heiso/macrolev/ref/lekker-switch-2.webp

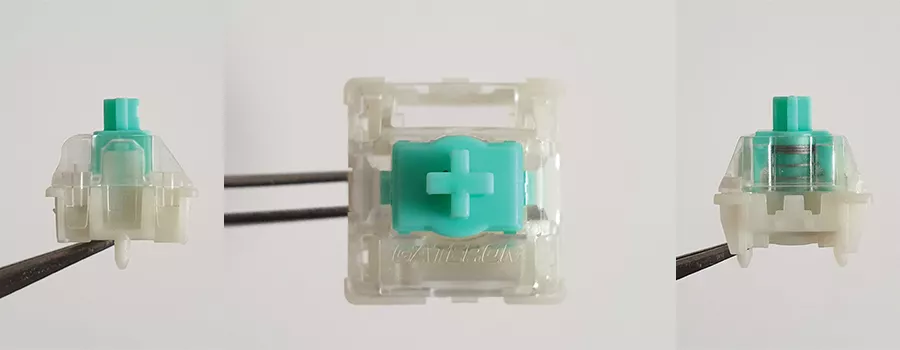
ref/lekker-switch-2.webp
