heiso/macrolev/ref/lekker-switch.png

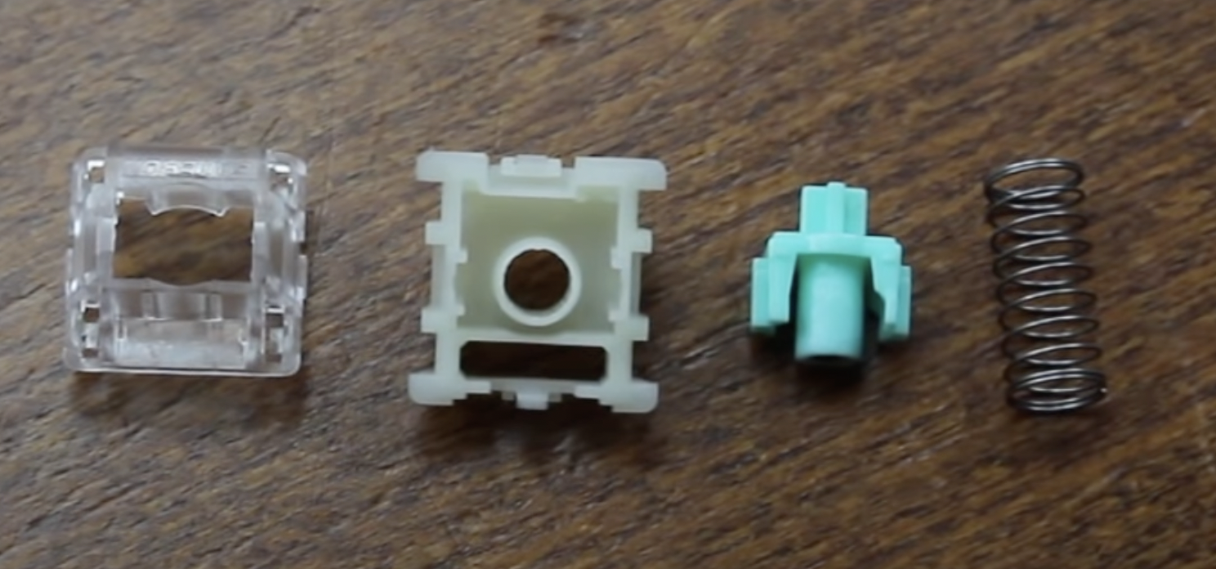
ref/lekker-switch.png
