heiso/macrolev/ref/Wooting-60HE/W60HE-01.jpg

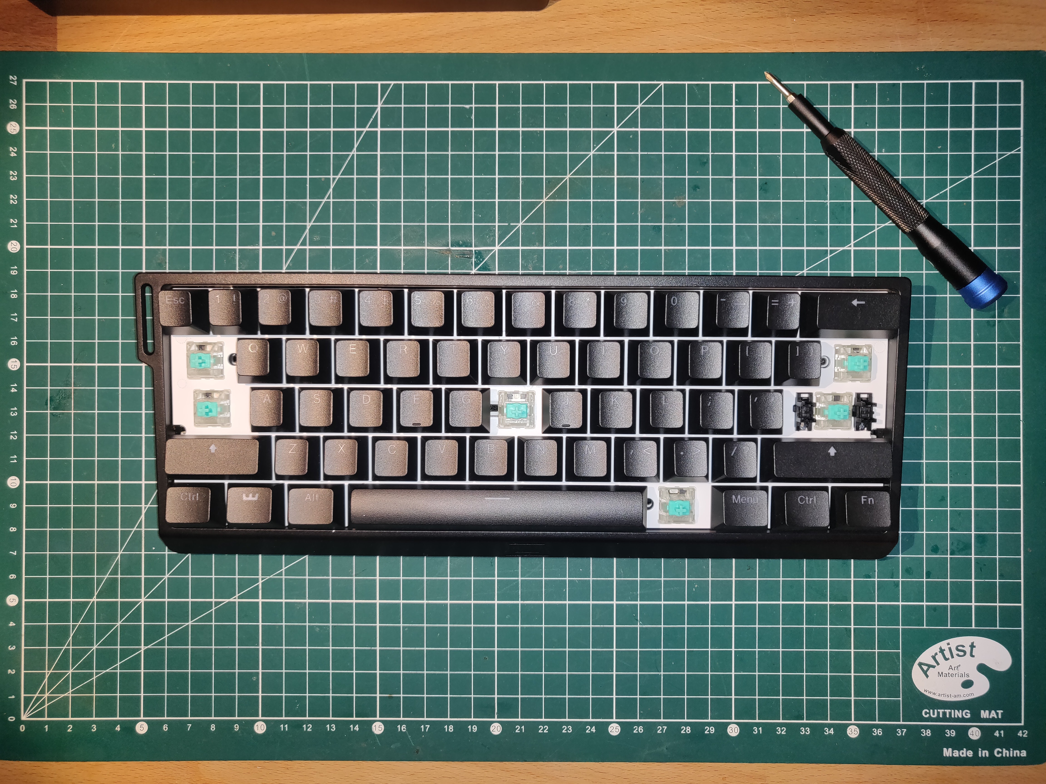
ref/Wooting-60HE/W60HE-01.jpg
