heiso/macrolev/ref/Wooting-60HE/W60HE-02.jpg

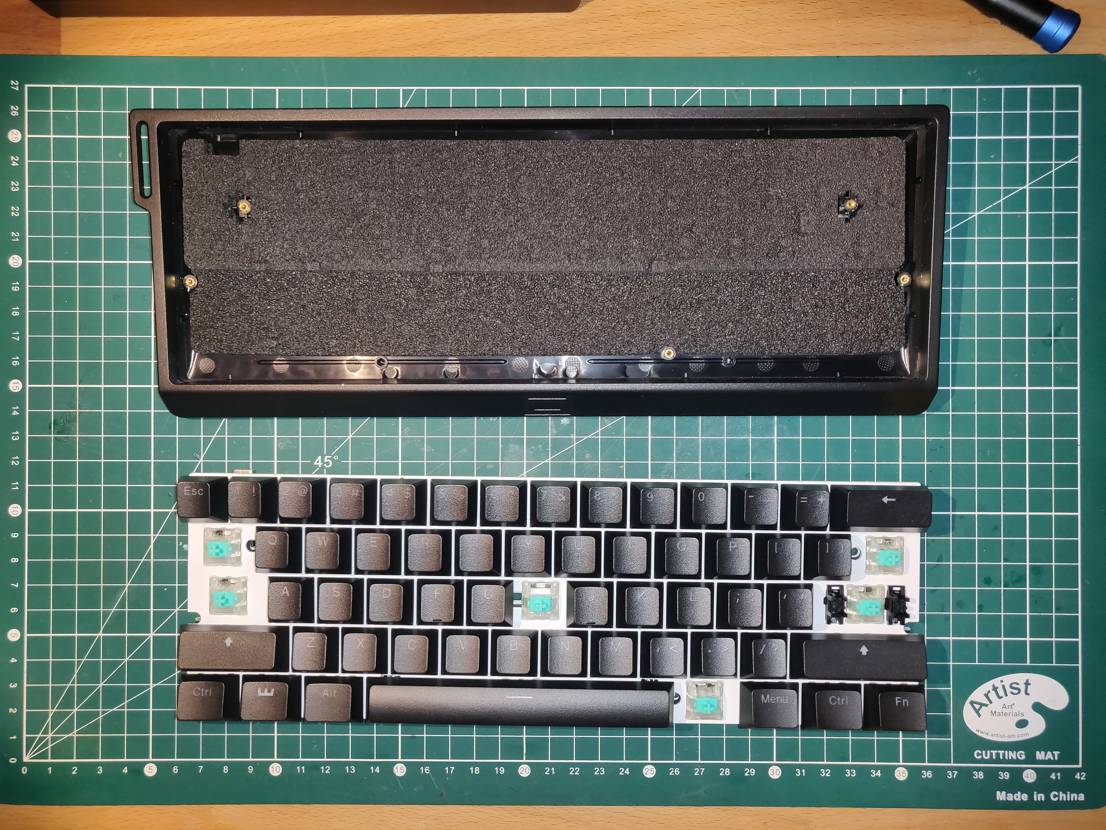
ref/Wooting-60HE/W60HE-02.jpg
