heiso/macrolev/ref/Wooting-60HE/W60HE-03.jpg

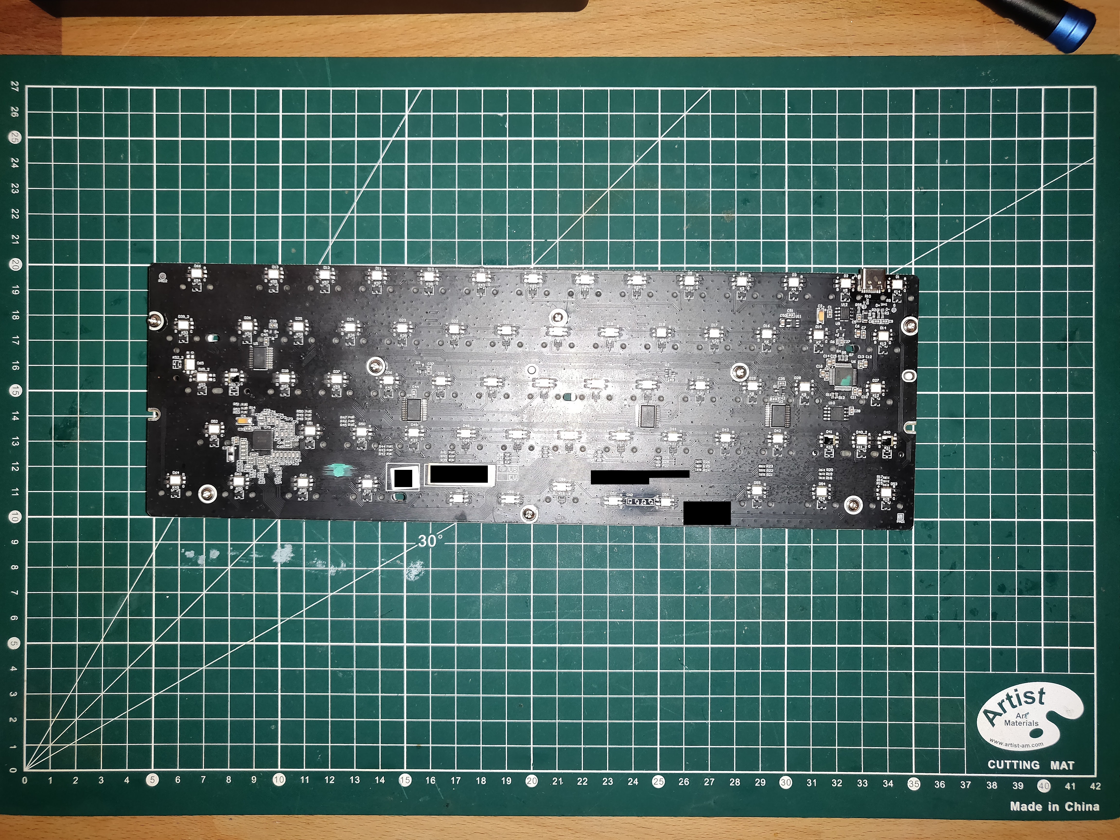
ref/Wooting-60HE/W60HE-03.jpg
