heiso/macrolev/ref/Wooting-60HE/W60HE-04.jpg

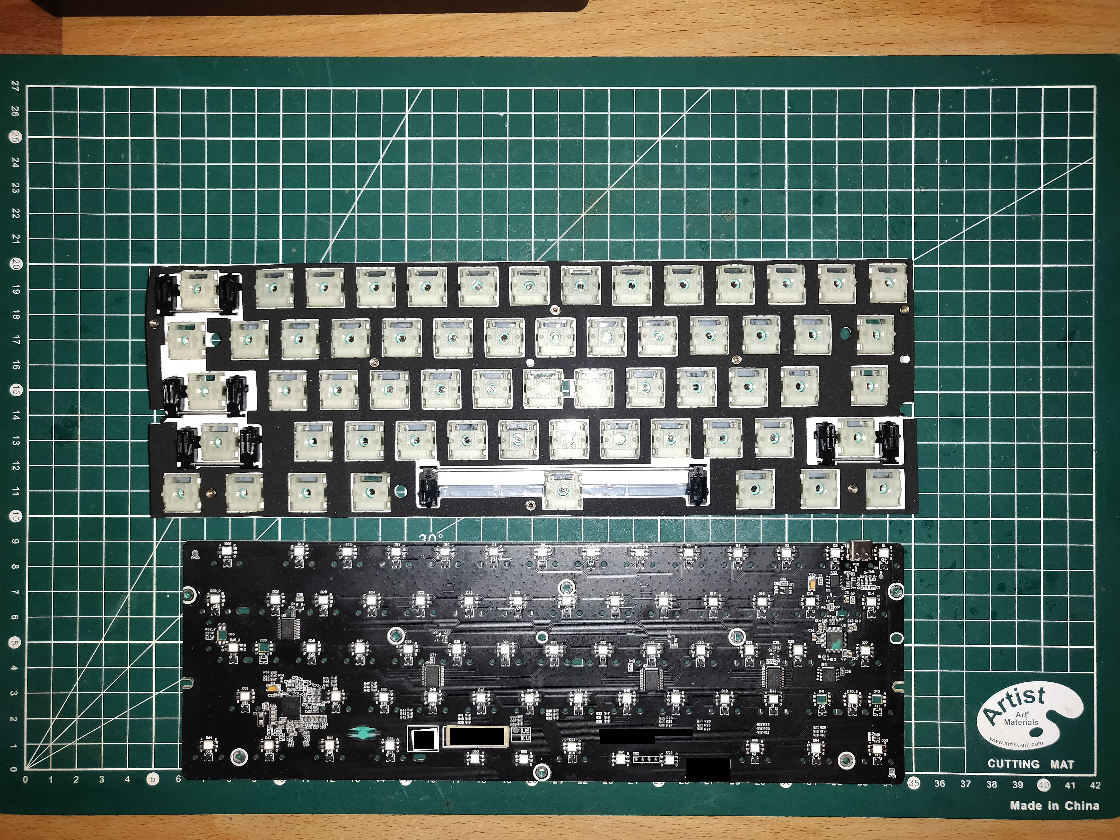
ref/Wooting-60HE/W60HE-04.jpg
