heiso/macrolev/ref/Wooting-60HE/W60HE-07.jpg

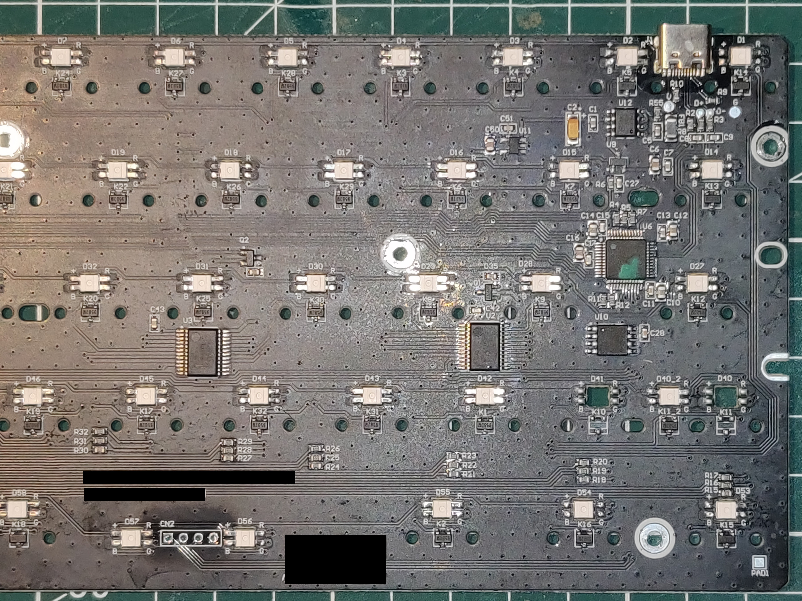
ref/Wooting-60HE/W60HE-07.jpg
