heiso/macrolev/ref/Wooting-60HE/W60HE-08.jpg

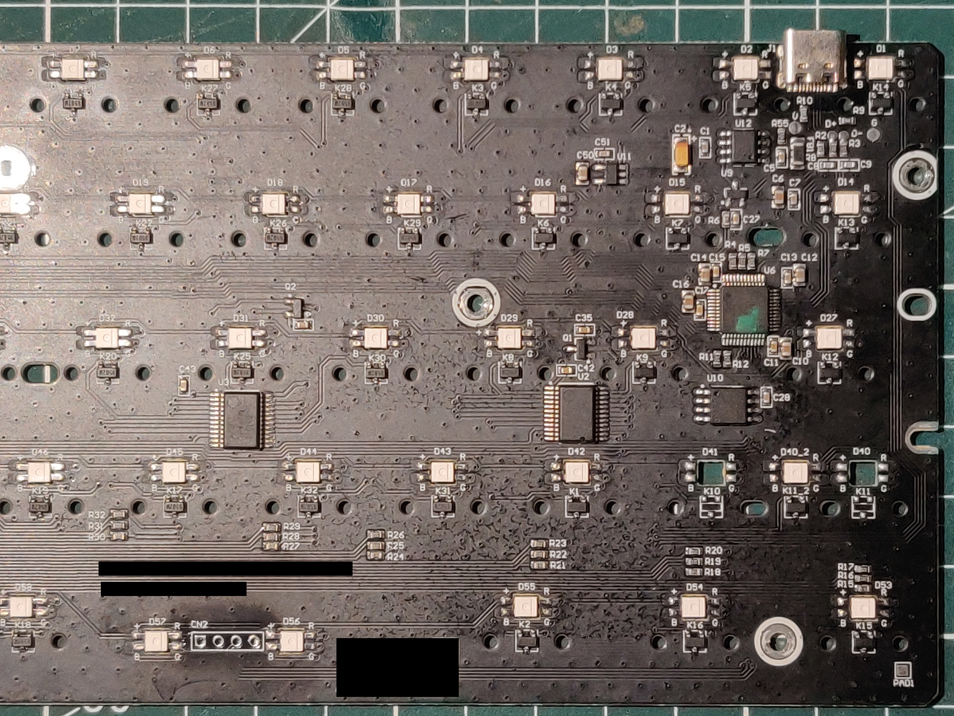
ref/Wooting-60HE/W60HE-08.jpg
