heiso/macrolev/ref/Wooting-60HE/W60HE-09.jpg

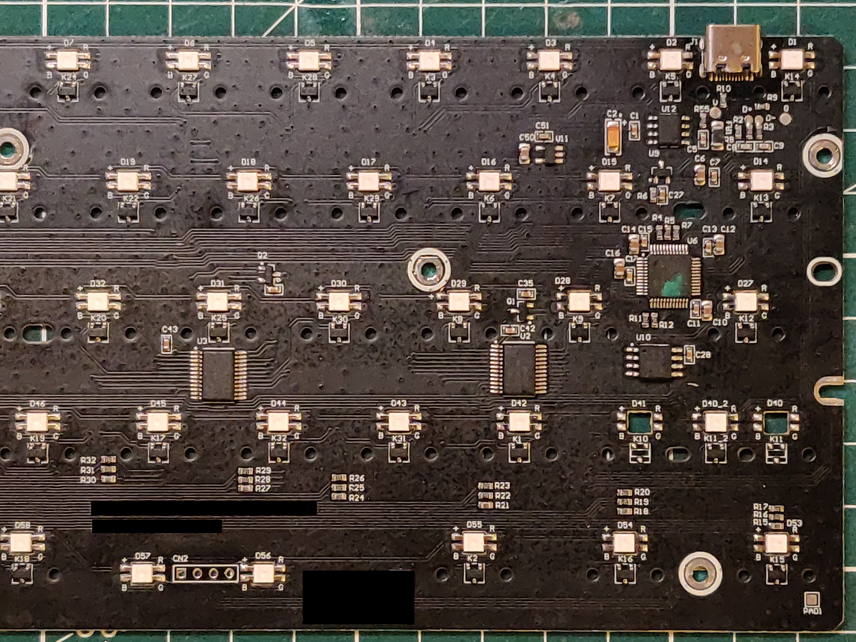
ref/Wooting-60HE/W60HE-09.jpg
