heiso/macrolev/ref/Wooting-60HE/W60HE-10.jpg

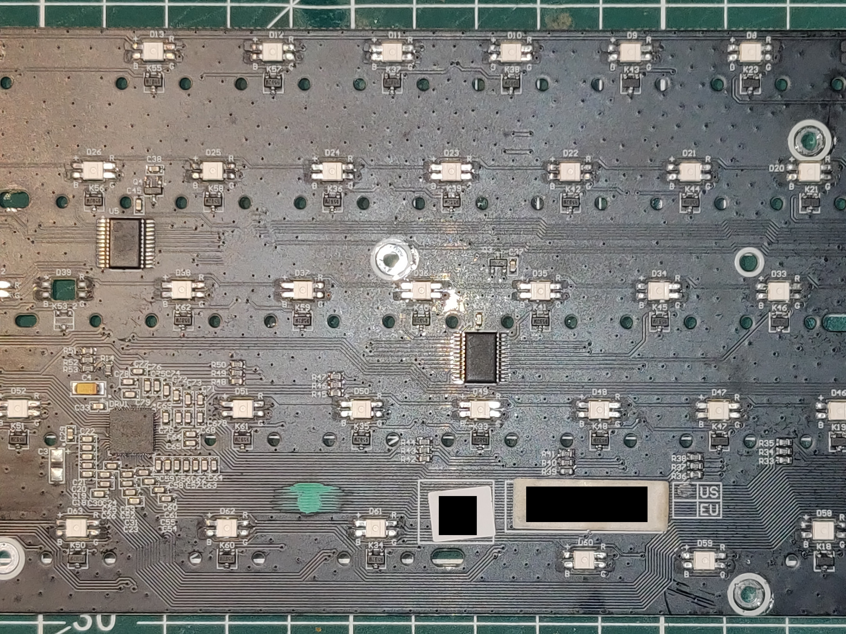
ref/Wooting-60HE/W60HE-10.jpg
