heiso/macrolev/ref/Wooting-60HE/W60HE-11.jpg

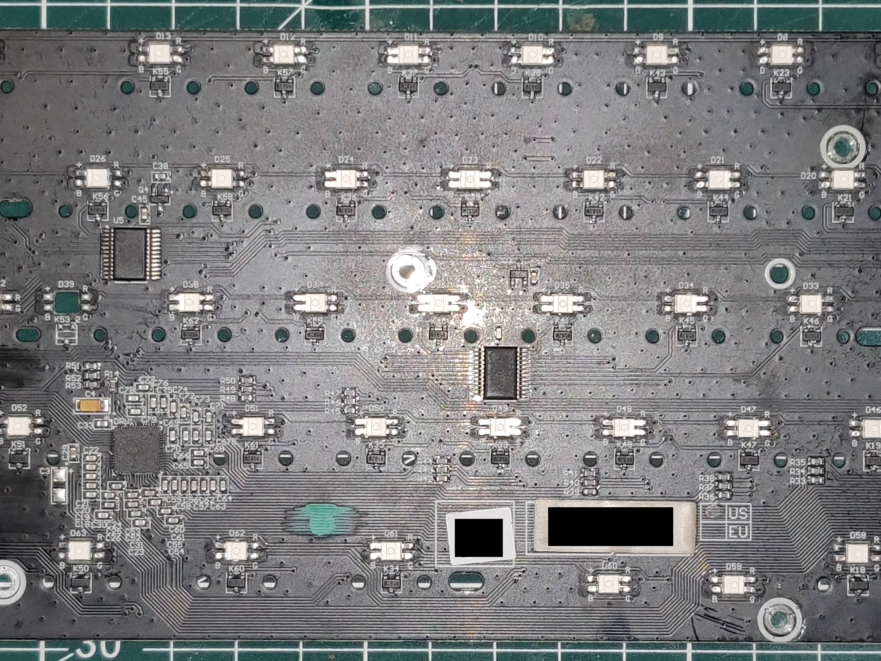
ref/Wooting-60HE/W60HE-11.jpg
