heiso/macrolev/ref/Wooting-60HE/W60HE-12.jpg

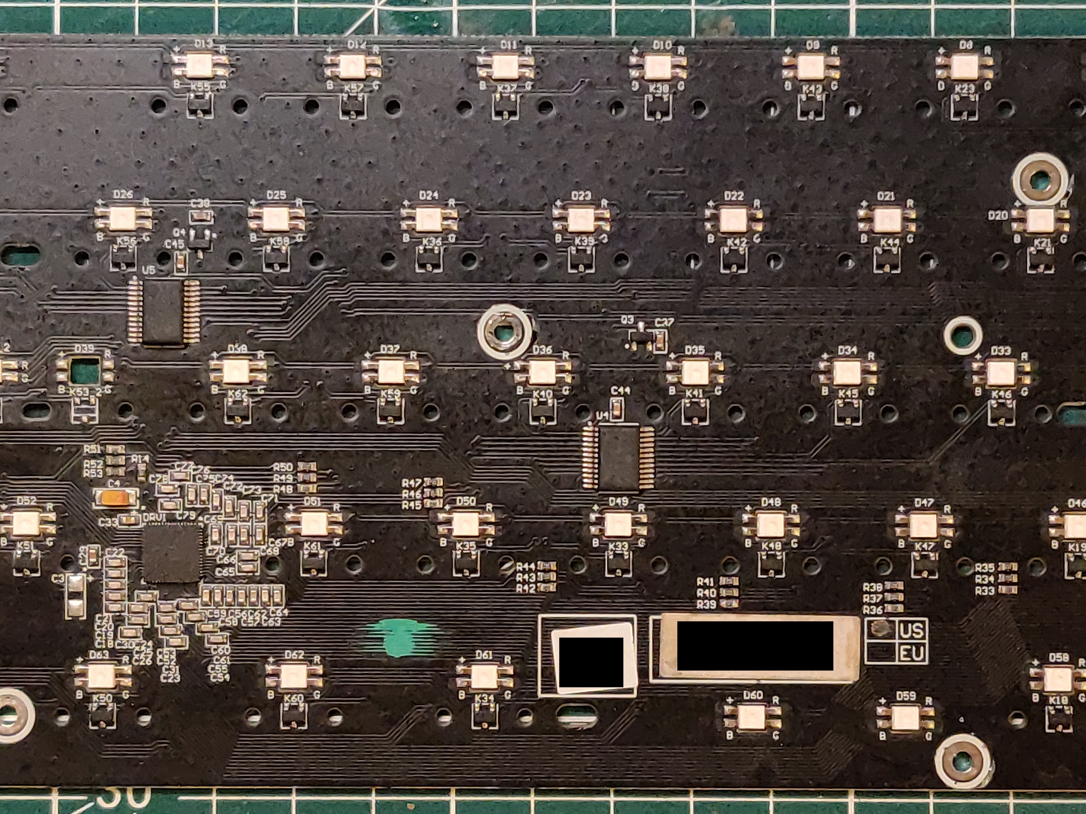
ref/Wooting-60HE/W60HE-12.jpg
