heiso/macrolev/ref/Wooting-60HE/W60HE-13.jpg

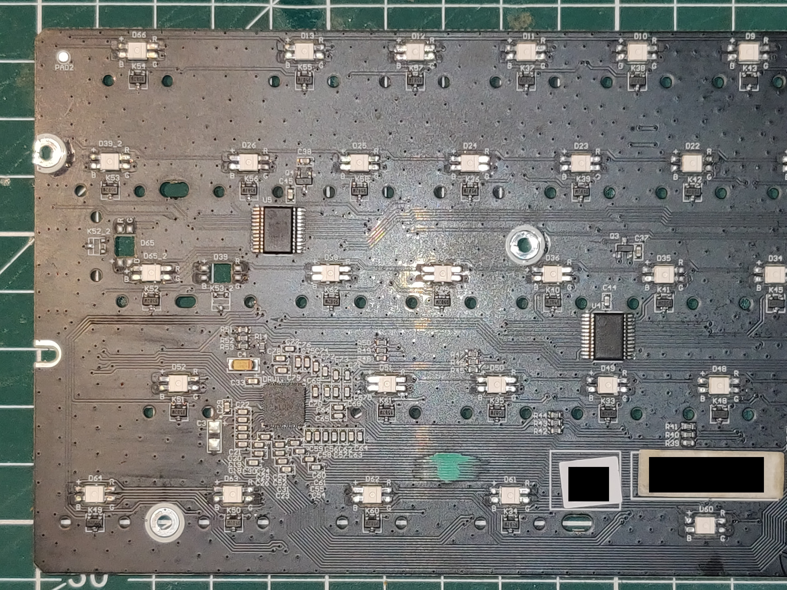
ref/Wooting-60HE/W60HE-13.jpg
