heiso/macrolev/ref/Wooting-60HE/W60HE-14.jpg

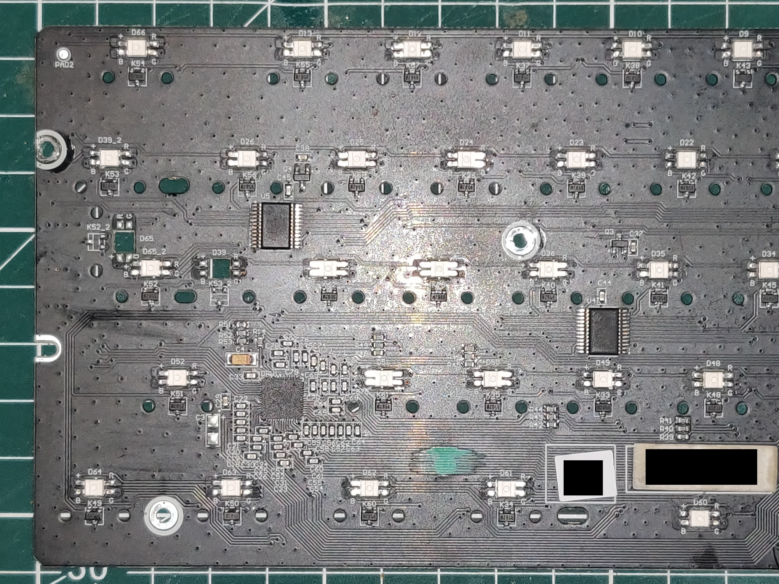
ref/Wooting-60HE/W60HE-14.jpg
