heiso/macrolev/ref/Wooting-60HE/W60HE-16.jpg

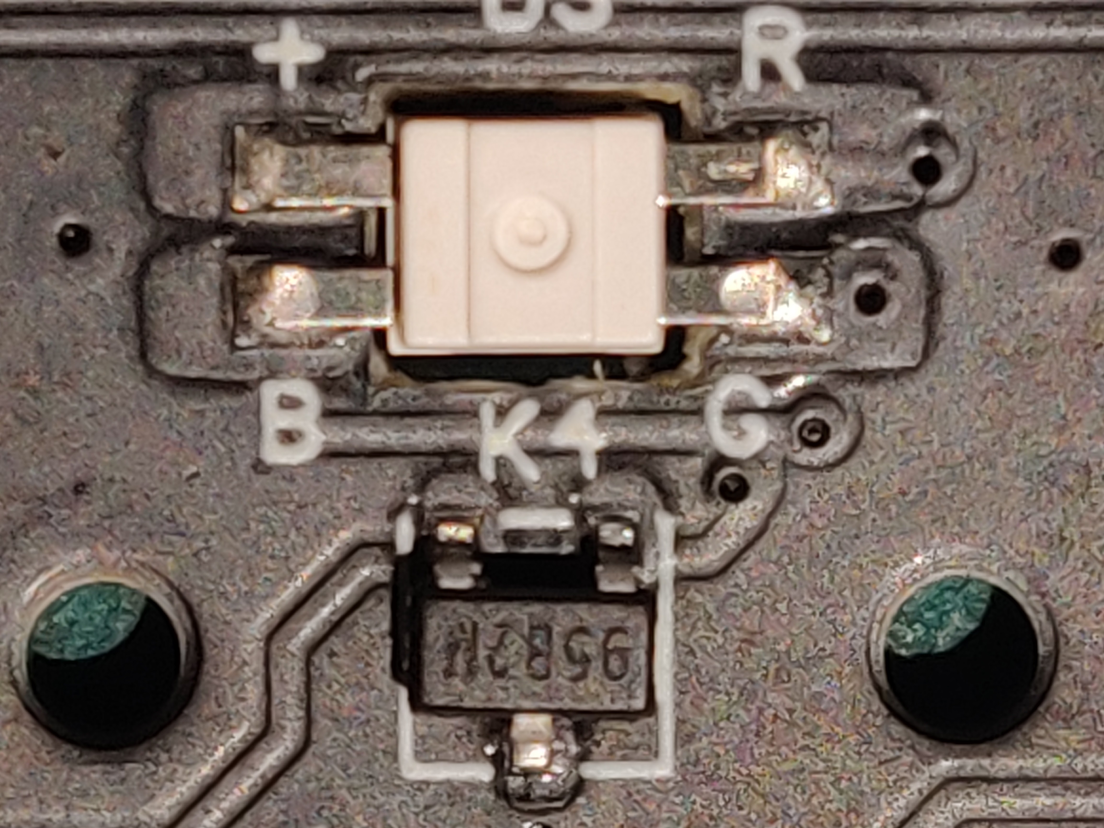
ref/Wooting-60HE/W60HE-16.jpg
