heiso/macrolev/ref/Wooting-60HE/W60HE-17.jpg

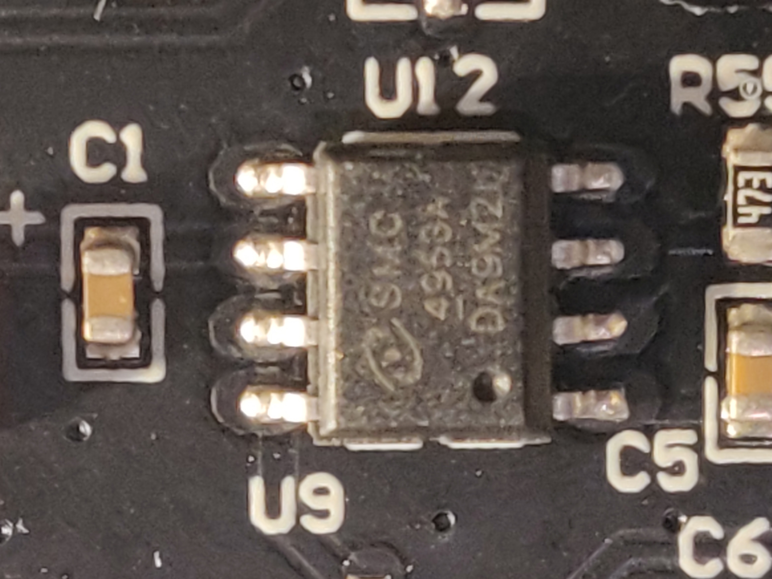
ref/Wooting-60HE/W60HE-17.jpg
