heiso/macrolev/ref/Wooting-60HE/W60HE-18.jpg

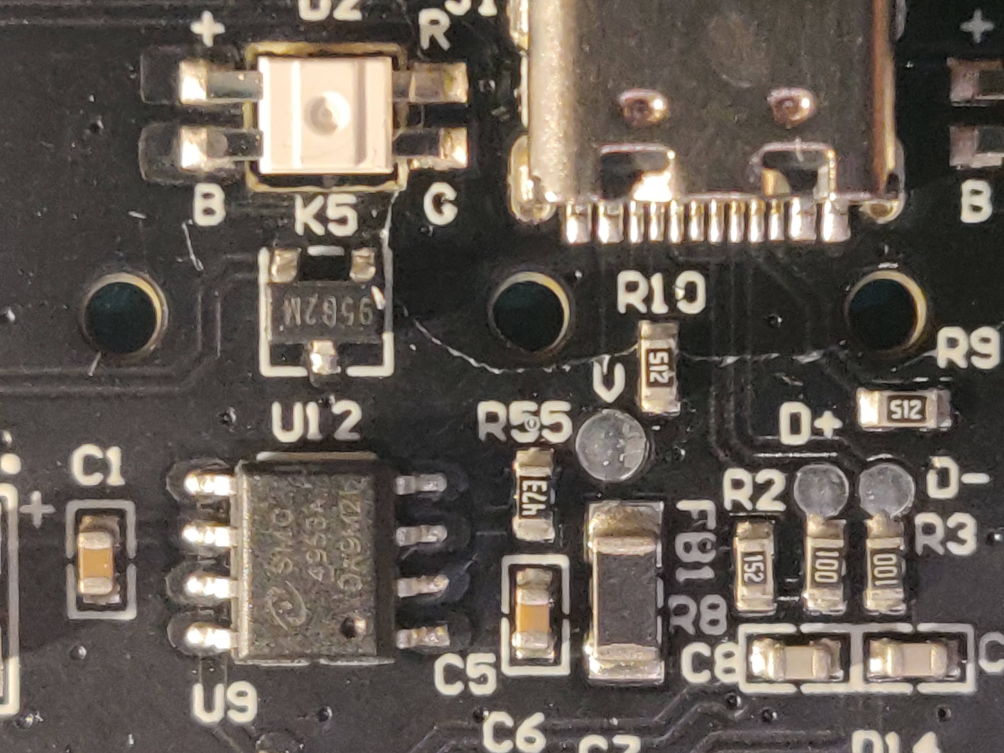
ref/Wooting-60HE/W60HE-18.jpg
