heiso/macrolev/ref/Wooting-60HE/W60HE-19.jpg

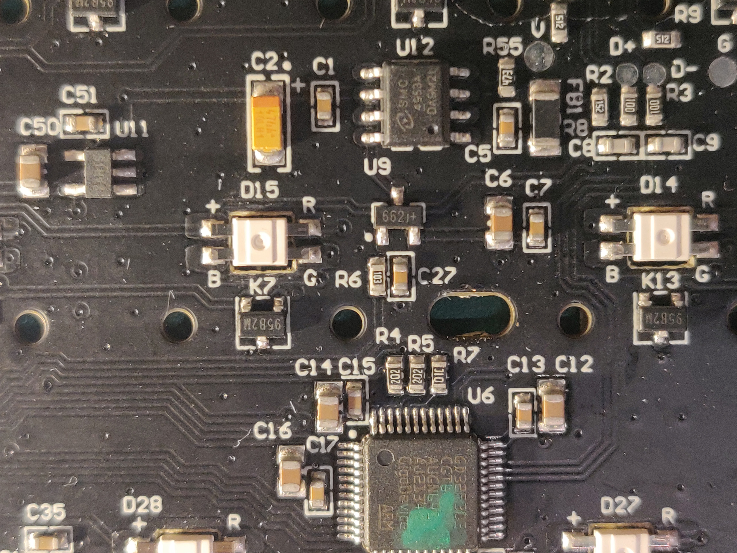
ref/Wooting-60HE/W60HE-19.jpg
