heiso/macrolev/ref/Wooting-60HE/W60HE-20.jpg

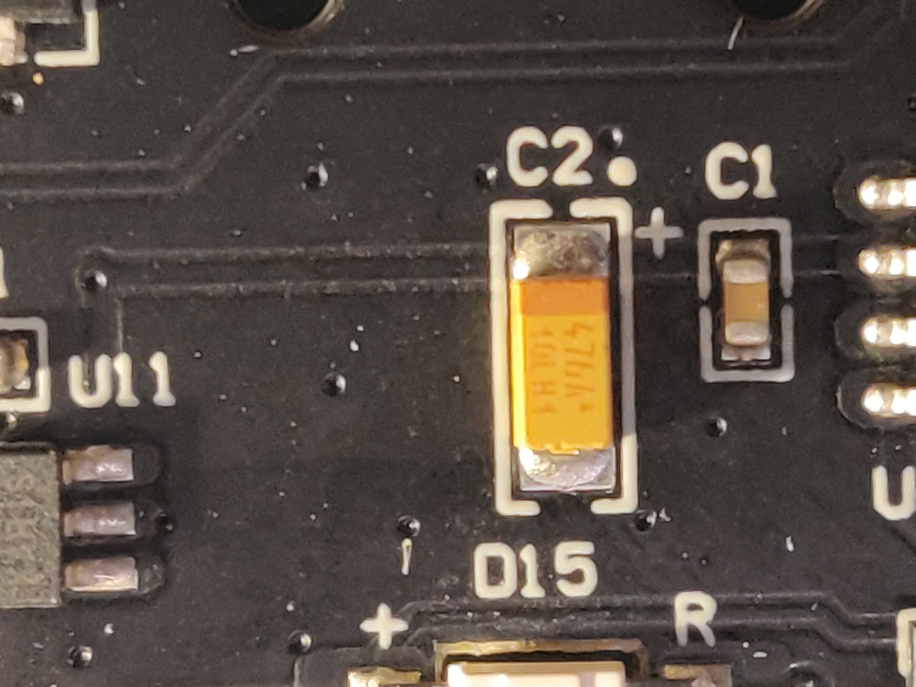
ref/Wooting-60HE/W60HE-20.jpg
