heiso/macrolev/ref/Wooting-60HE/W60HE-21.jpg

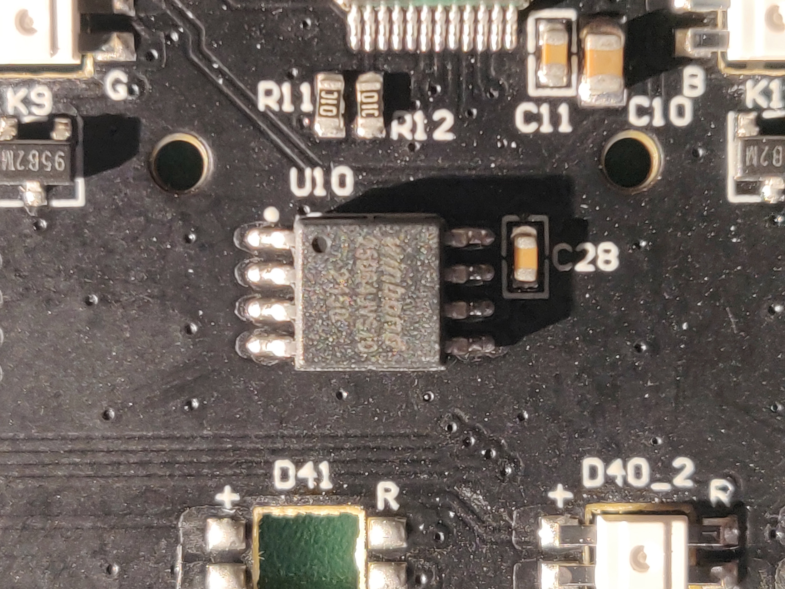
ref/Wooting-60HE/W60HE-21.jpg
