heiso/macrolev/ref/Wooting-60HE/W60HE-22.jpg

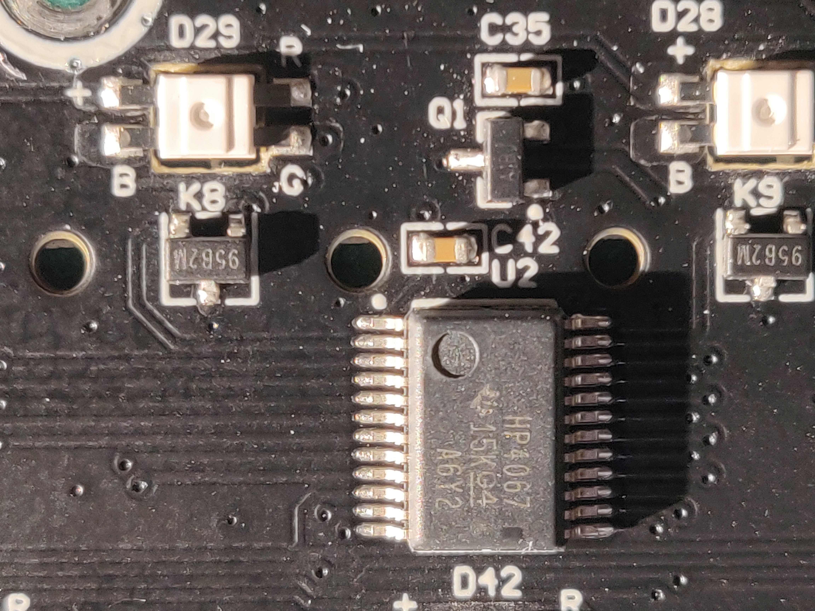
ref/Wooting-60HE/W60HE-22.jpg
