heiso/macrolev/ref/Wooting-60HE/W60HE-23.jpg

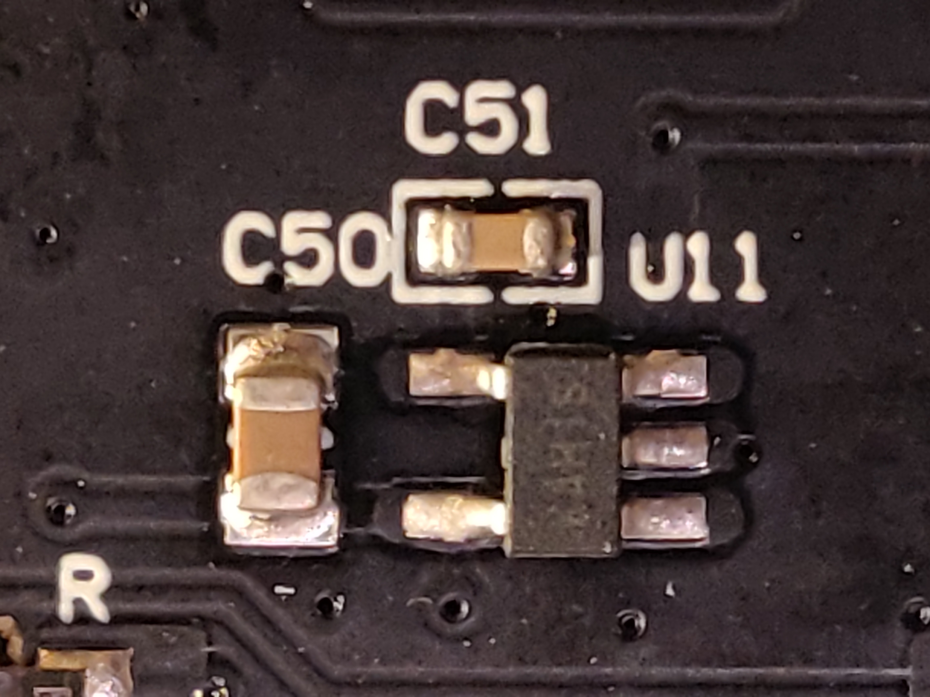
ref/Wooting-60HE/W60HE-23.jpg
