heiso/macrolev/ref/Wooting-60HE/W60HE-24.jpg

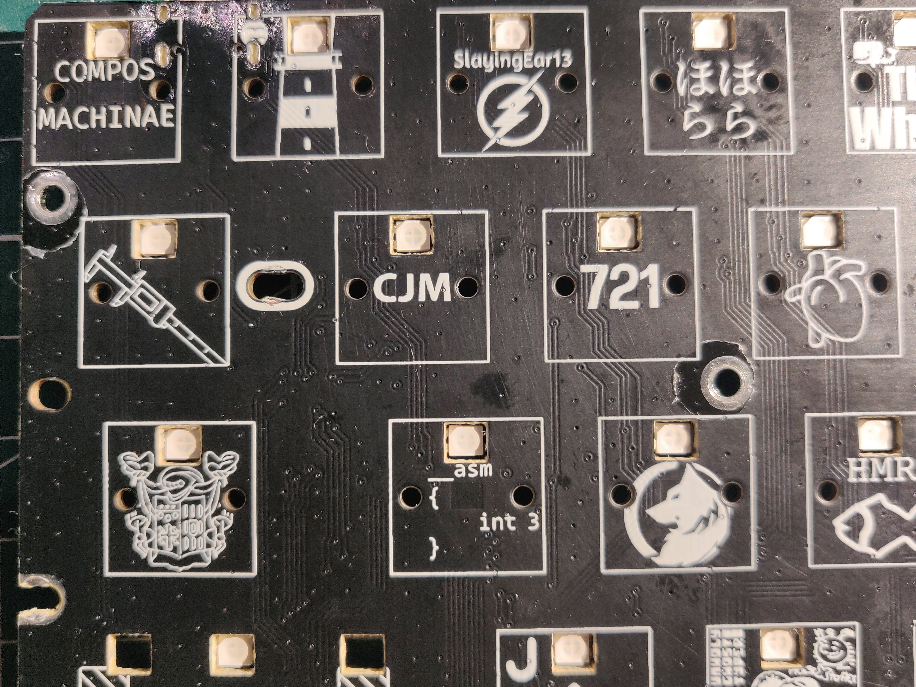
ref/Wooting-60HE/W60HE-24.jpg
