heiso/macrolev/ref/Wooting-60HE/W60HE-25.jpg

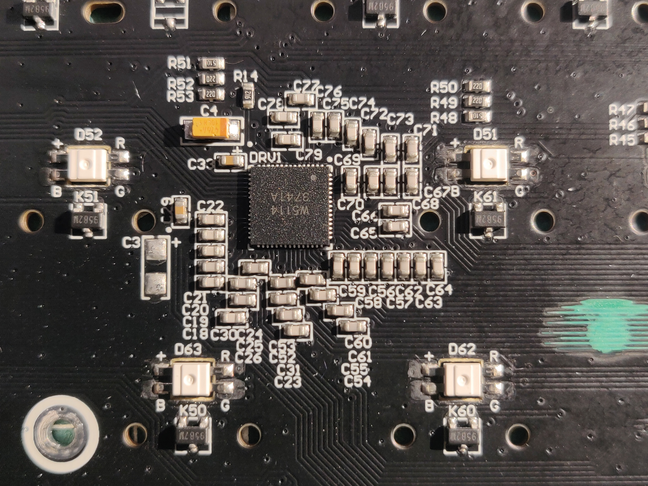
ref/Wooting-60HE/W60HE-25.jpg
