heiso/macrolev/ref/Wooting-60HE/W60HE-26.jpg

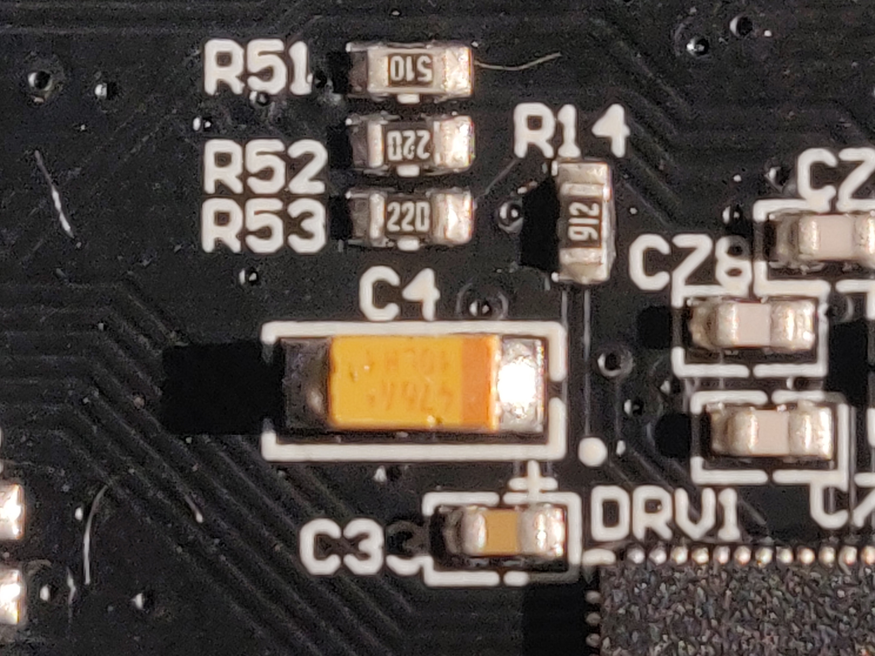
ref/Wooting-60HE/W60HE-26.jpg
