heiso/macrolev/ref/Wooting-60HE/W60HE-27.jpg

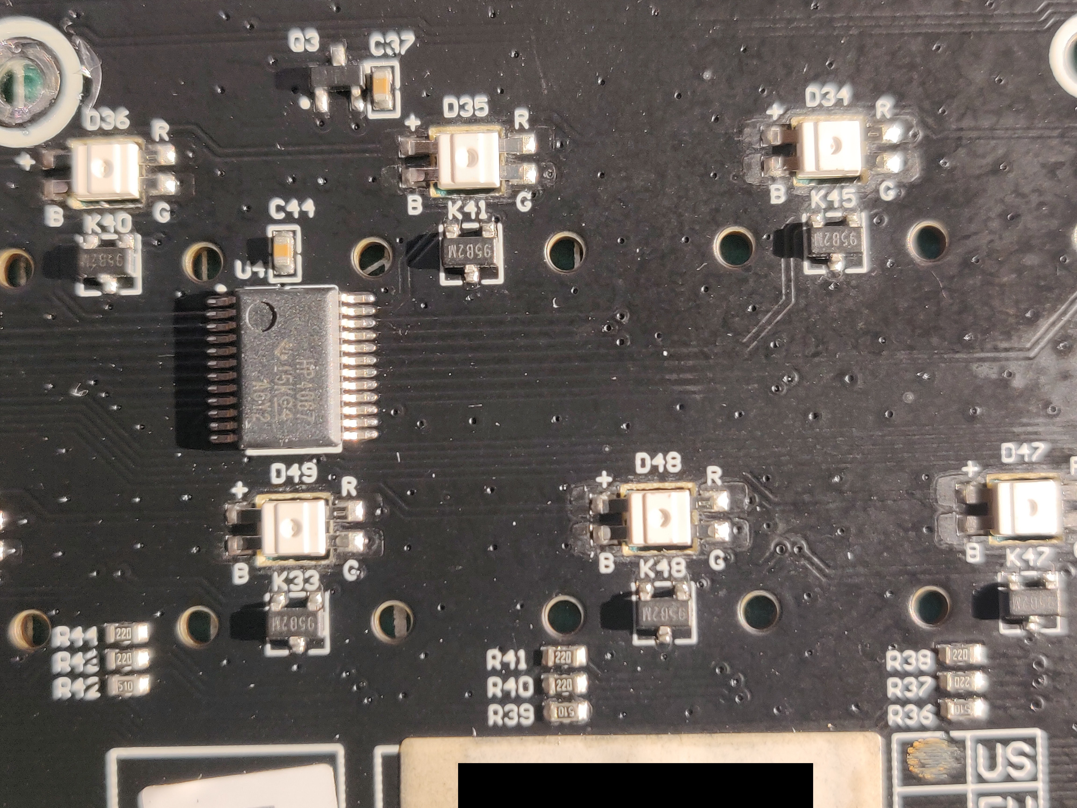
ref/Wooting-60HE/W60HE-27.jpg
