heiso/macrolev/ref/Wooting-60HE/W60HE-28.jpg

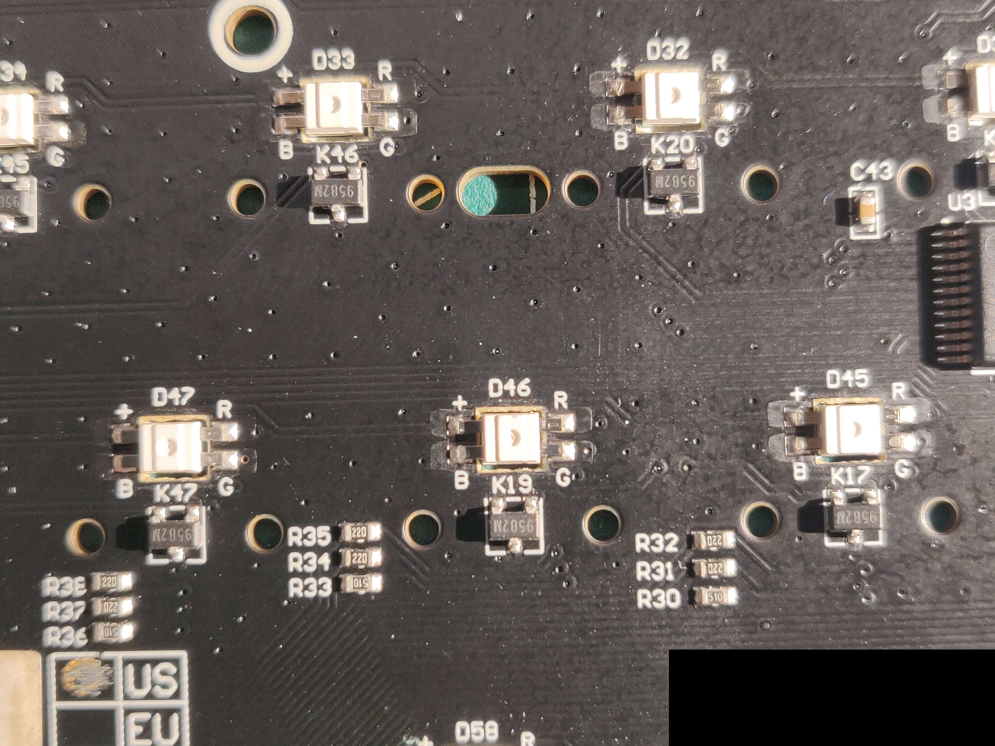
ref/Wooting-60HE/W60HE-28.jpg
