heiso/macrolev/ref/Wooting-60HE/W60HE-29.jpg

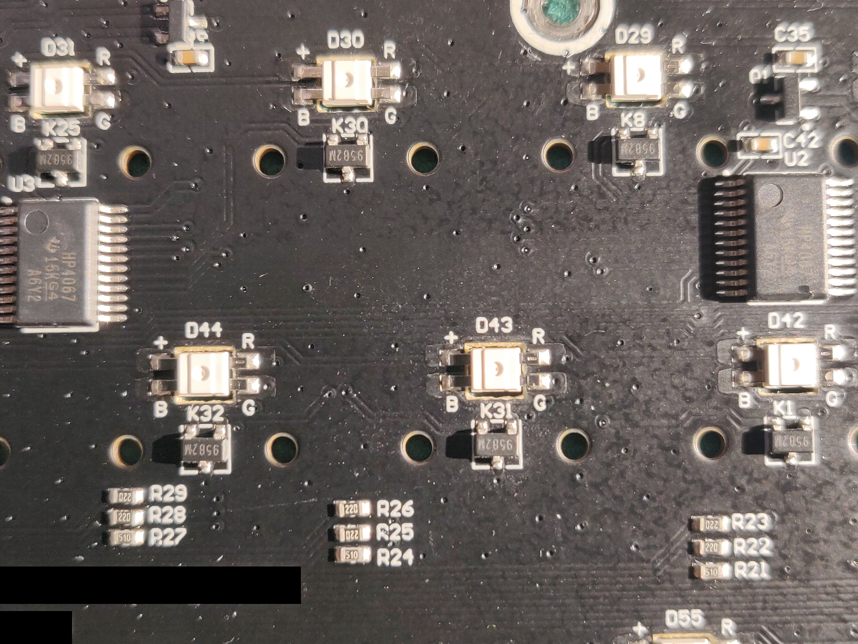
ref/Wooting-60HE/W60HE-29.jpg
