heiso/macrolev/ref/Wooting-60HE/W60HE-30.jpg

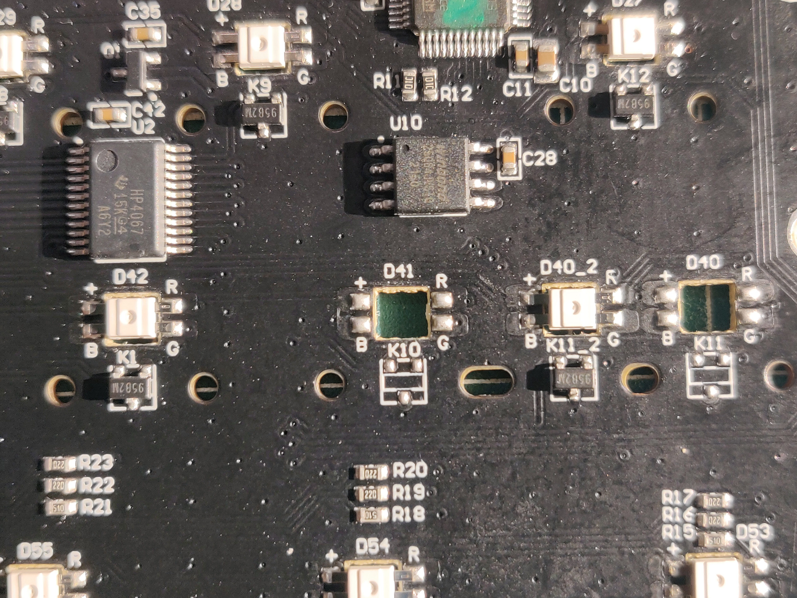
ref/Wooting-60HE/W60HE-30.jpg
