heiso/macrolev/ref/Wooting-60HE/W60HE-31.jpg

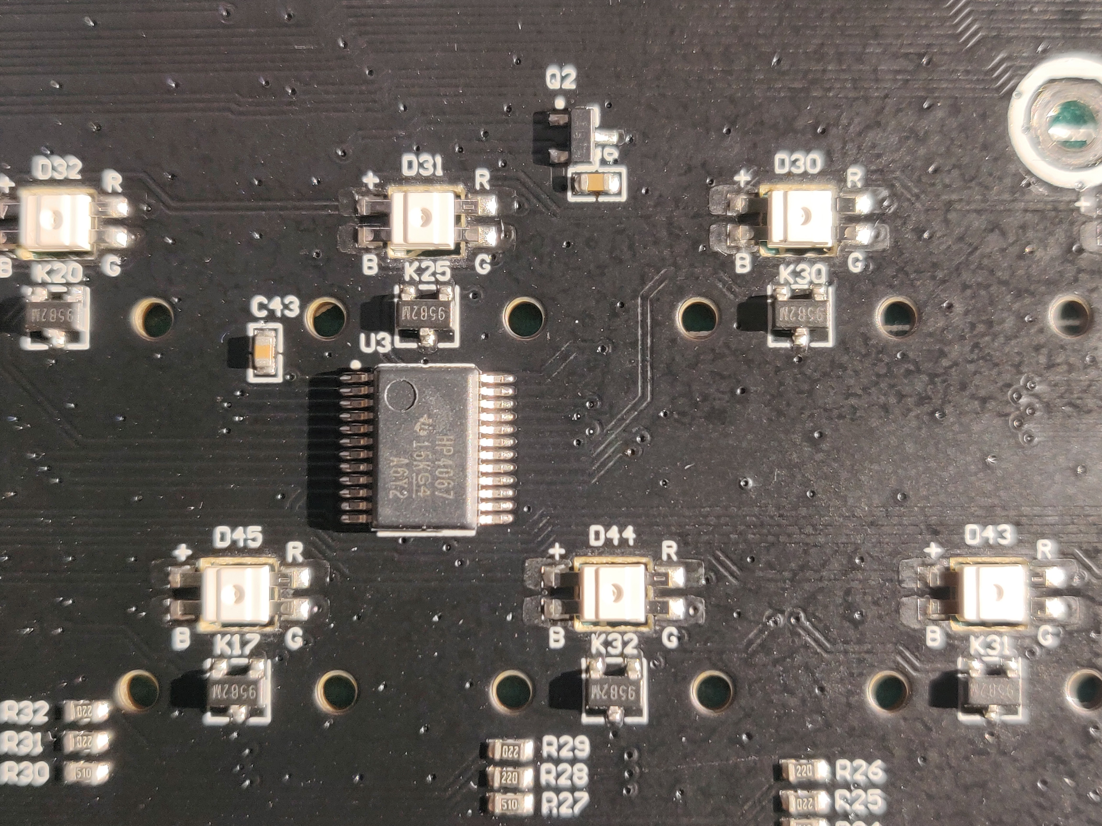
ref/Wooting-60HE/W60HE-31.jpg
