heiso/macrolev/ref/Wooting-60HE/W60HE-32.jpg

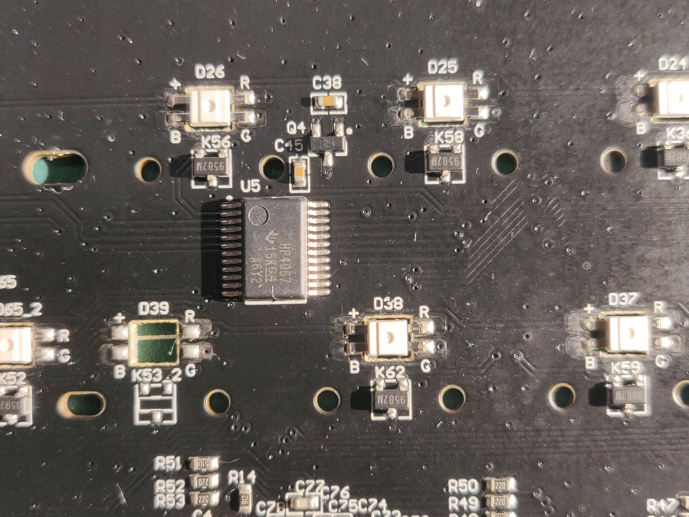
ref/Wooting-60HE/W60HE-32.jpg
