heiso/macrolev/ref/Wooting-60HE/W60HE-33.jpg

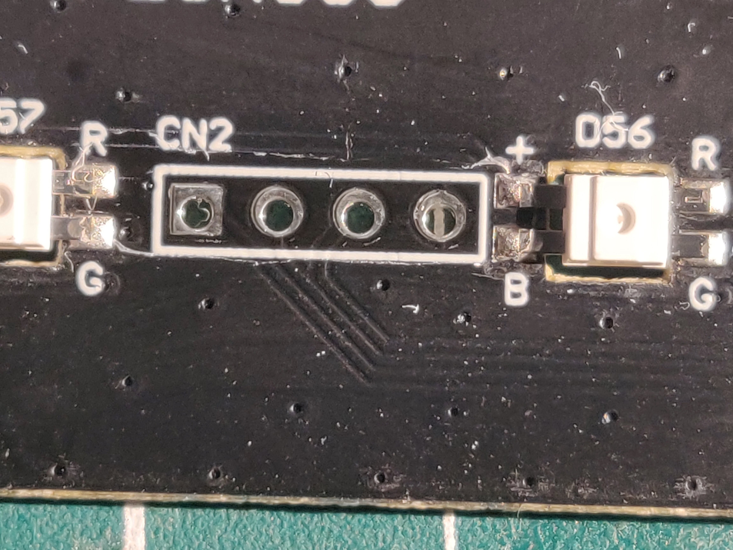
ref/Wooting-60HE/W60HE-33.jpg
