heiso/macrolev/ref/Wooting-60HE/W60HE-34.jpg

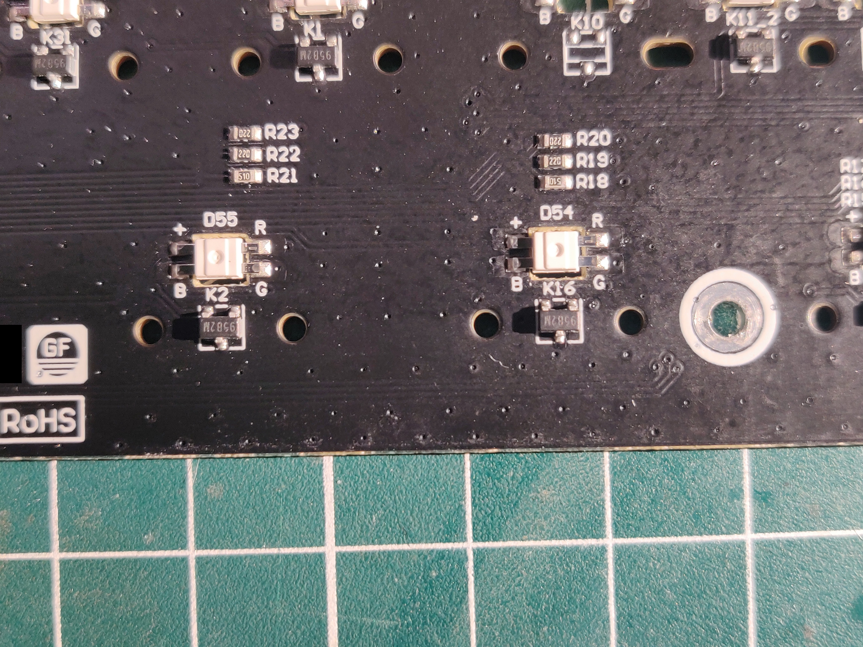
ref/Wooting-60HE/W60HE-34.jpg
