heiso/macrolev/ref/Wooting-60HE/W60HE-35.jpg

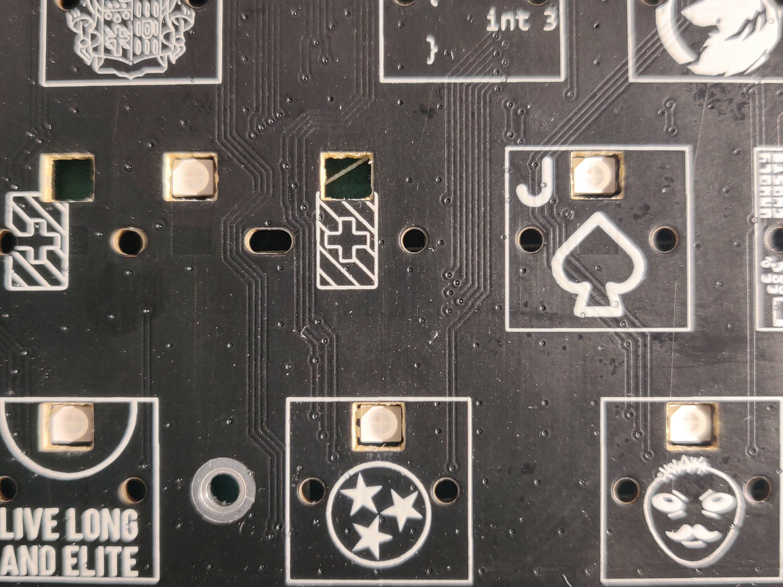
ref/Wooting-60HE/W60HE-35.jpg
