heiso/macrolev/ref/Wooting-60HE/W60HE-36.jpg

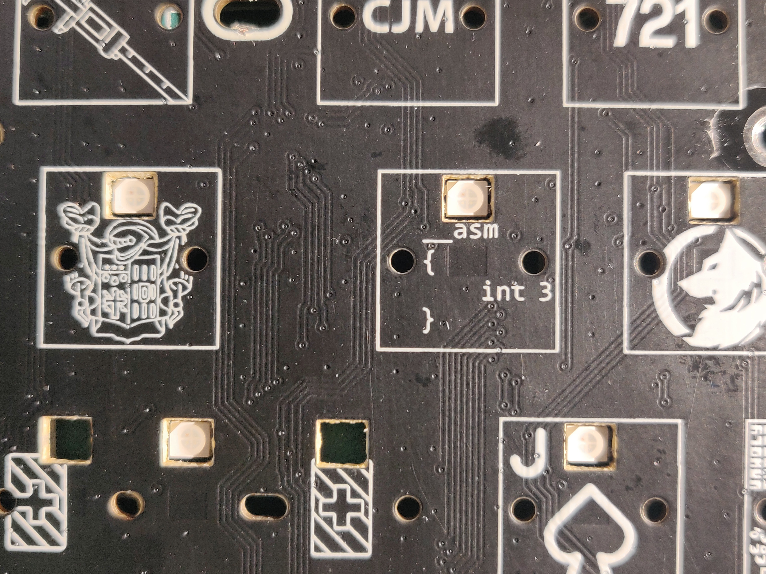
ref/Wooting-60HE/W60HE-36.jpg
