heiso/macrolev/ref/Wooting-60HE/W60HE-37.jpg

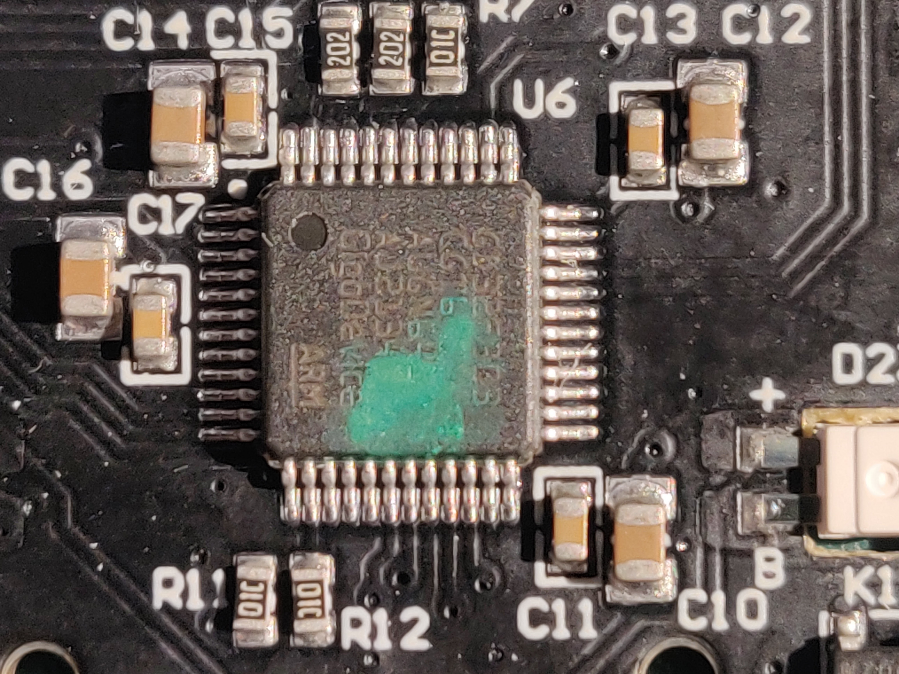
ref/Wooting-60HE/W60HE-37.jpg
