heiso/macrolev/ref/Wooting-60HE/W60HE-38.jpg

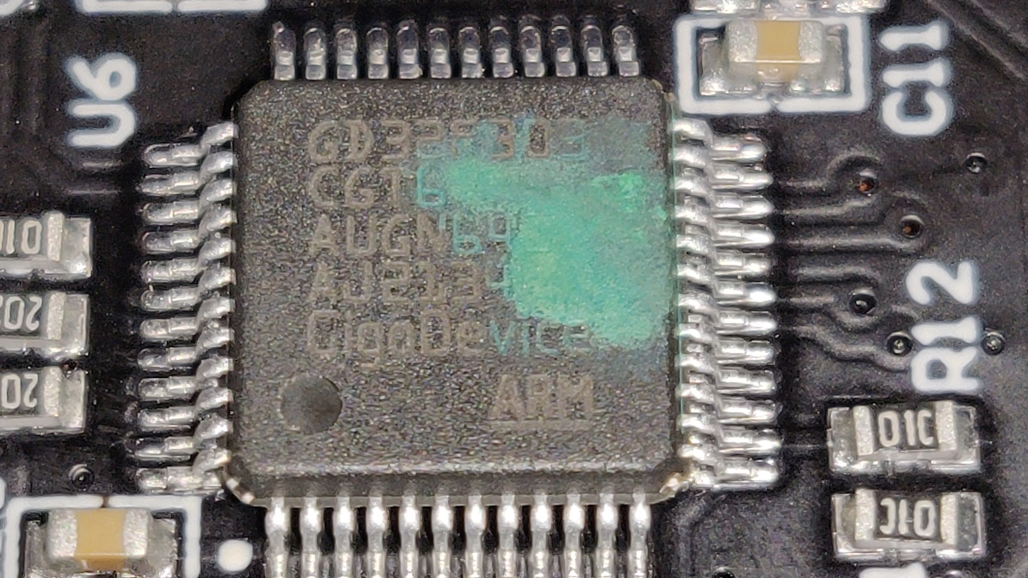
ref/Wooting-60HE/W60HE-38.jpg
